secolive/AtmelICE-Octopus/JTAG-MINI_ADAPTER/JTAG-MINI-ADAPTER_Doc_revA1/JTAG-MINI-ADAPTER.pdf

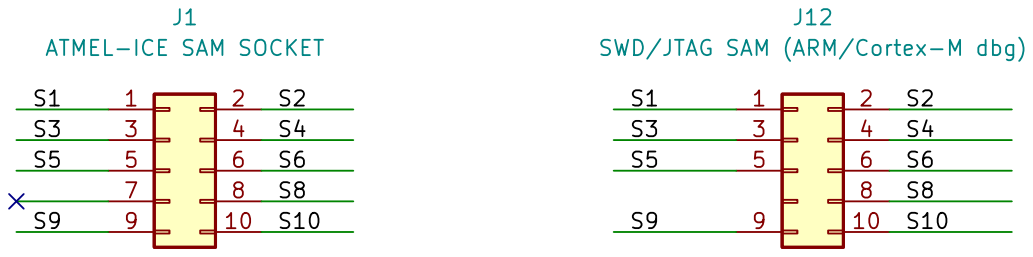
[picture p15: page 1]

J12 SWD/JTAG SAM (ARM/Cortex-M dbg) 1

JTAG 50mil to 100mil adapter
File: JTAG-MINI-ADAPTER.kicad_sch Sheet: / Licensed under CERN-OHL-W v2 Notably suitable for Arduino DUE

Id: 1/1 Title: JTAG-MINI-ADAPTER
