secolive/AtmelICE-Octopus/JTAG-MINI_ADAPTER/JTAG-MINI-ADAPTER_Doc_revA1/JTAG-MINI-ADAPTER-drill_map.pdf

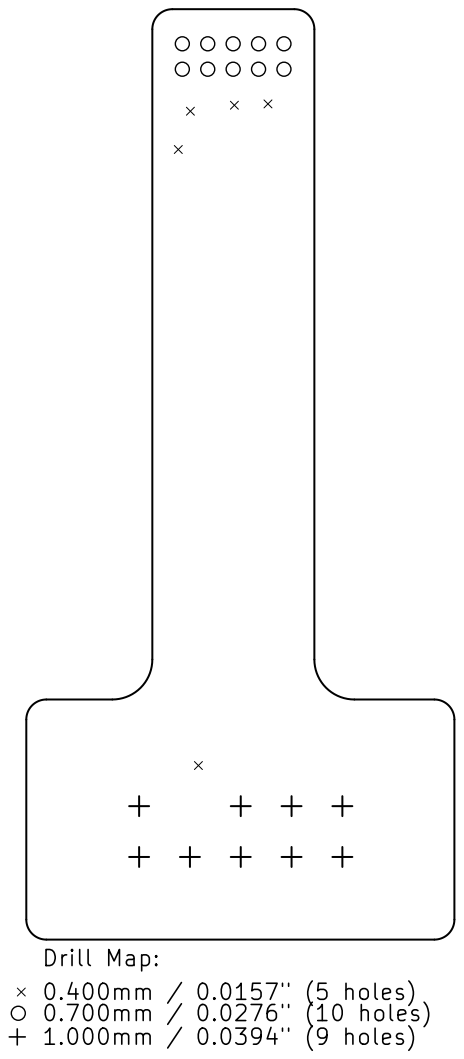
[picture p26: page 1]
