secolive/AtmelICE-Octopus/JTAG-MINI_ADAPTER/JTAG-MINI-ADAPTER_Doc_revA1/JTAG-MINI-ADAPTER-Edge_Cuts.pdf

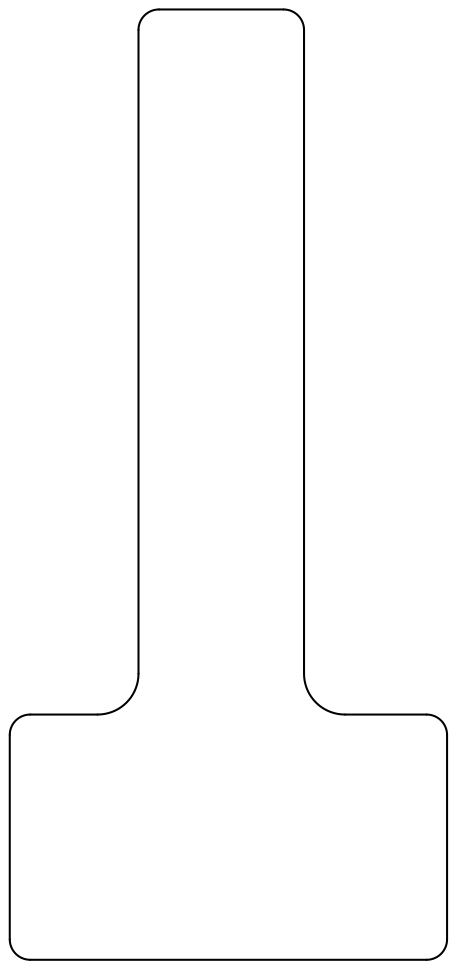
[picture p27: page 1]
