secolive/AtmelICE-Octopus/JTAG-MINI_ADAPTER/JTAG-MINI-ADAPTER_Doc_revA1/JTAG-MINI-ADAPTER-F_Cu.pdf

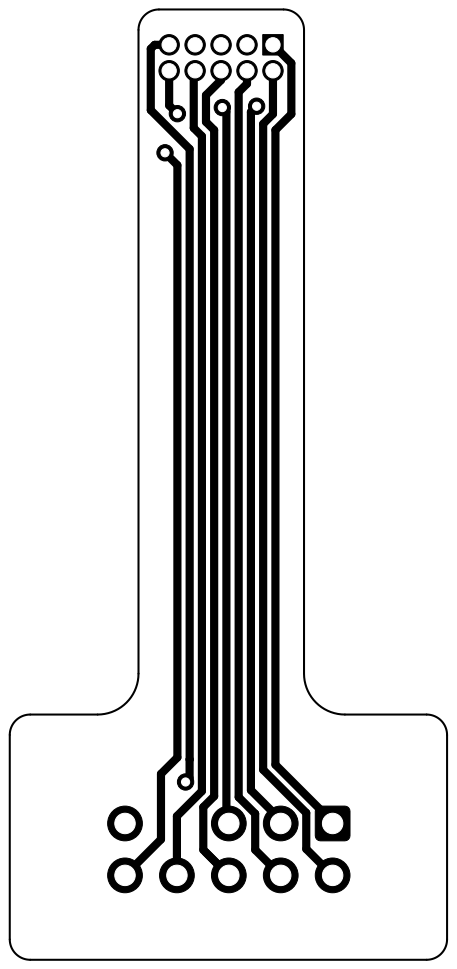
[picture p28: page 1]
