secolive/AtmelICE-Octopus/JTAG-MINI_ADAPTER/JTAG-MINI-ADAPTER_Doc_revA1/JTAG-MINI-ADAPTER-F_Silkscreen.pdf

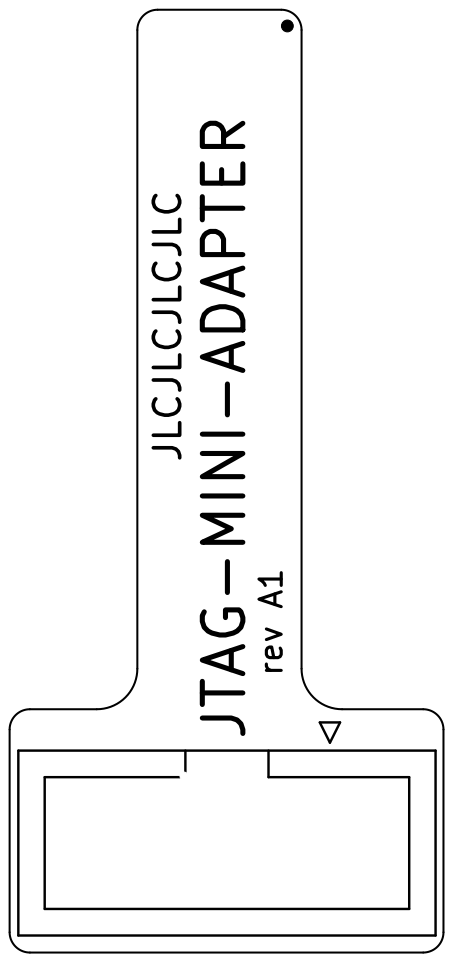
[picture p29: page 1]

JTAG-MINI-ADAPTER rev A1 JLCJLCJLCJLC
